aelde/kalwtummad2/model/pic/view1.jpeg

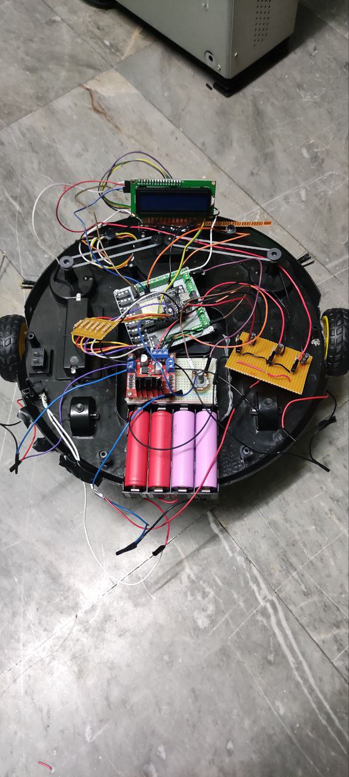
model/pic/view1.jpeg
