aelde/kalwtummad2/model/pic/view.jpeg

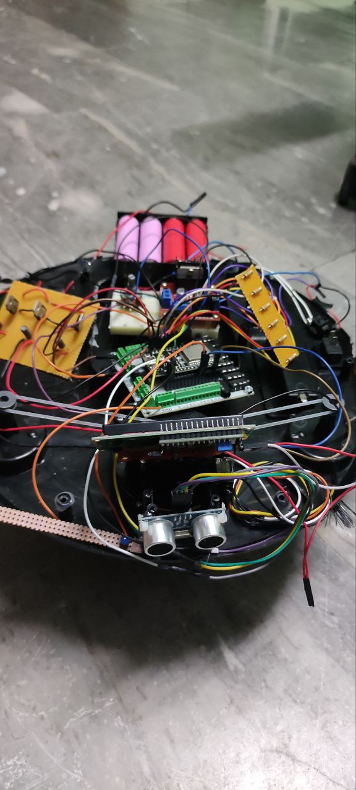
model/pic/view.jpeg
